noahrichards213/Interactive-chessboard/rev3/8x8/8x8.kicad_sch

## KiCad design rev3/8x8/8x8.kicad_sch (2026-08-15)

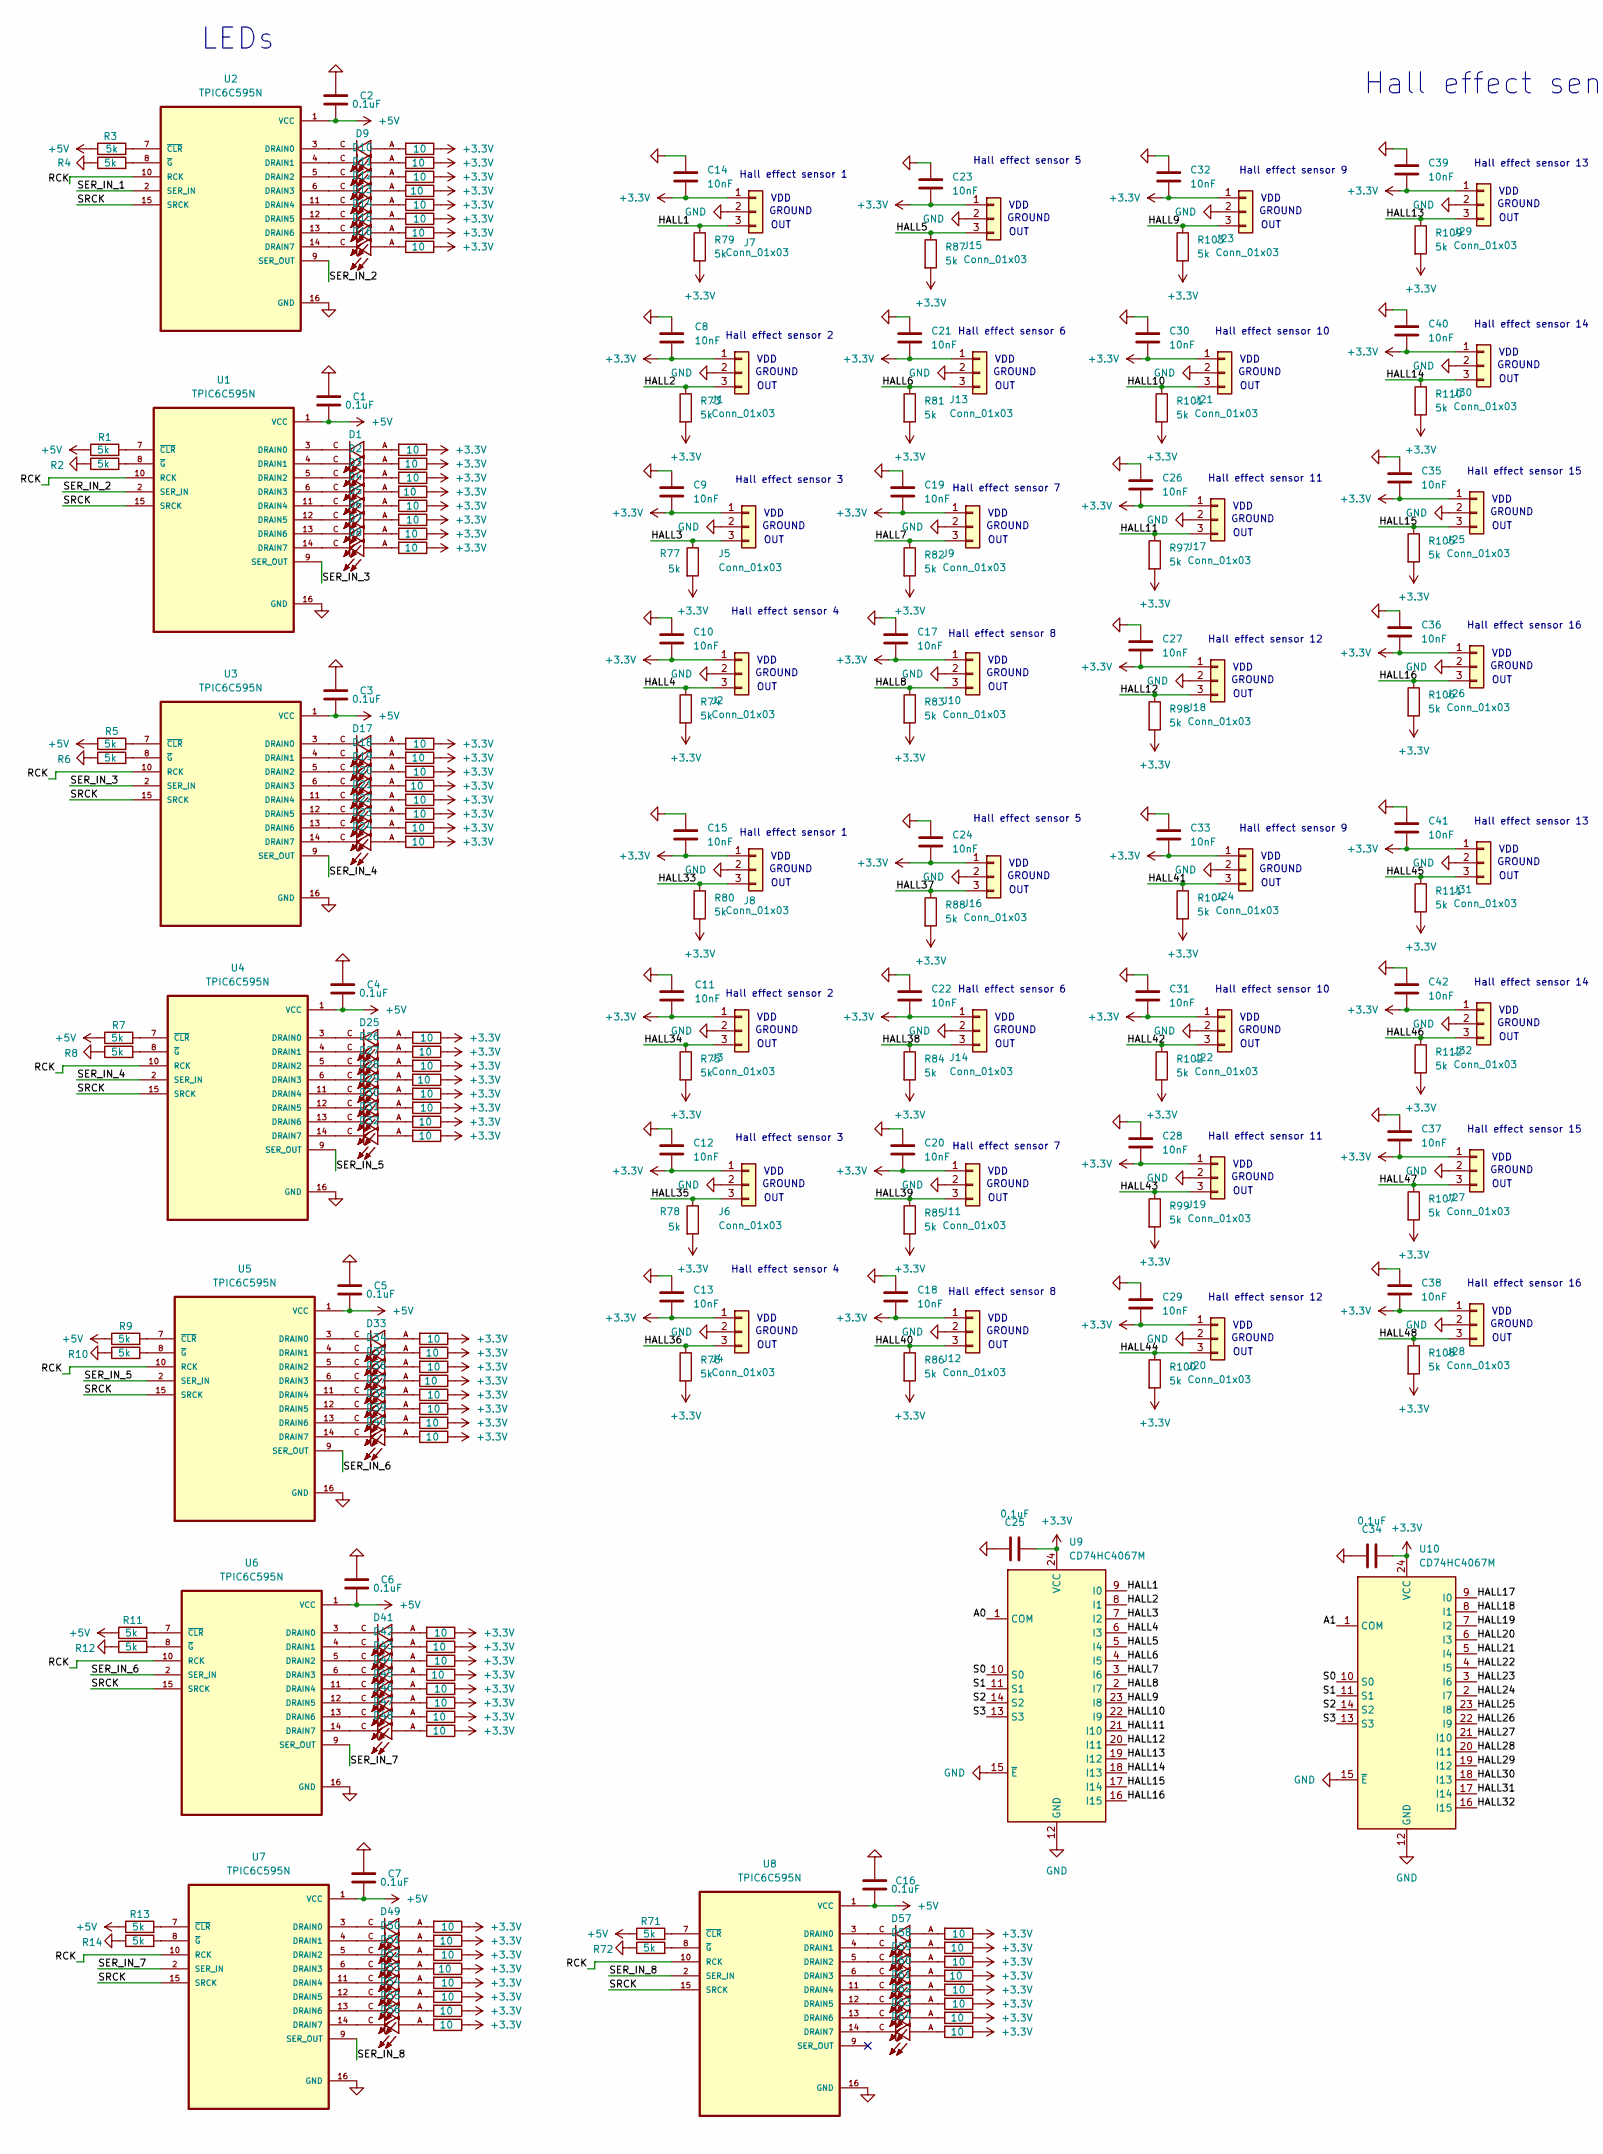
[picture p5: schematic 8x8.kicad_sch, part in row 1, column 1]

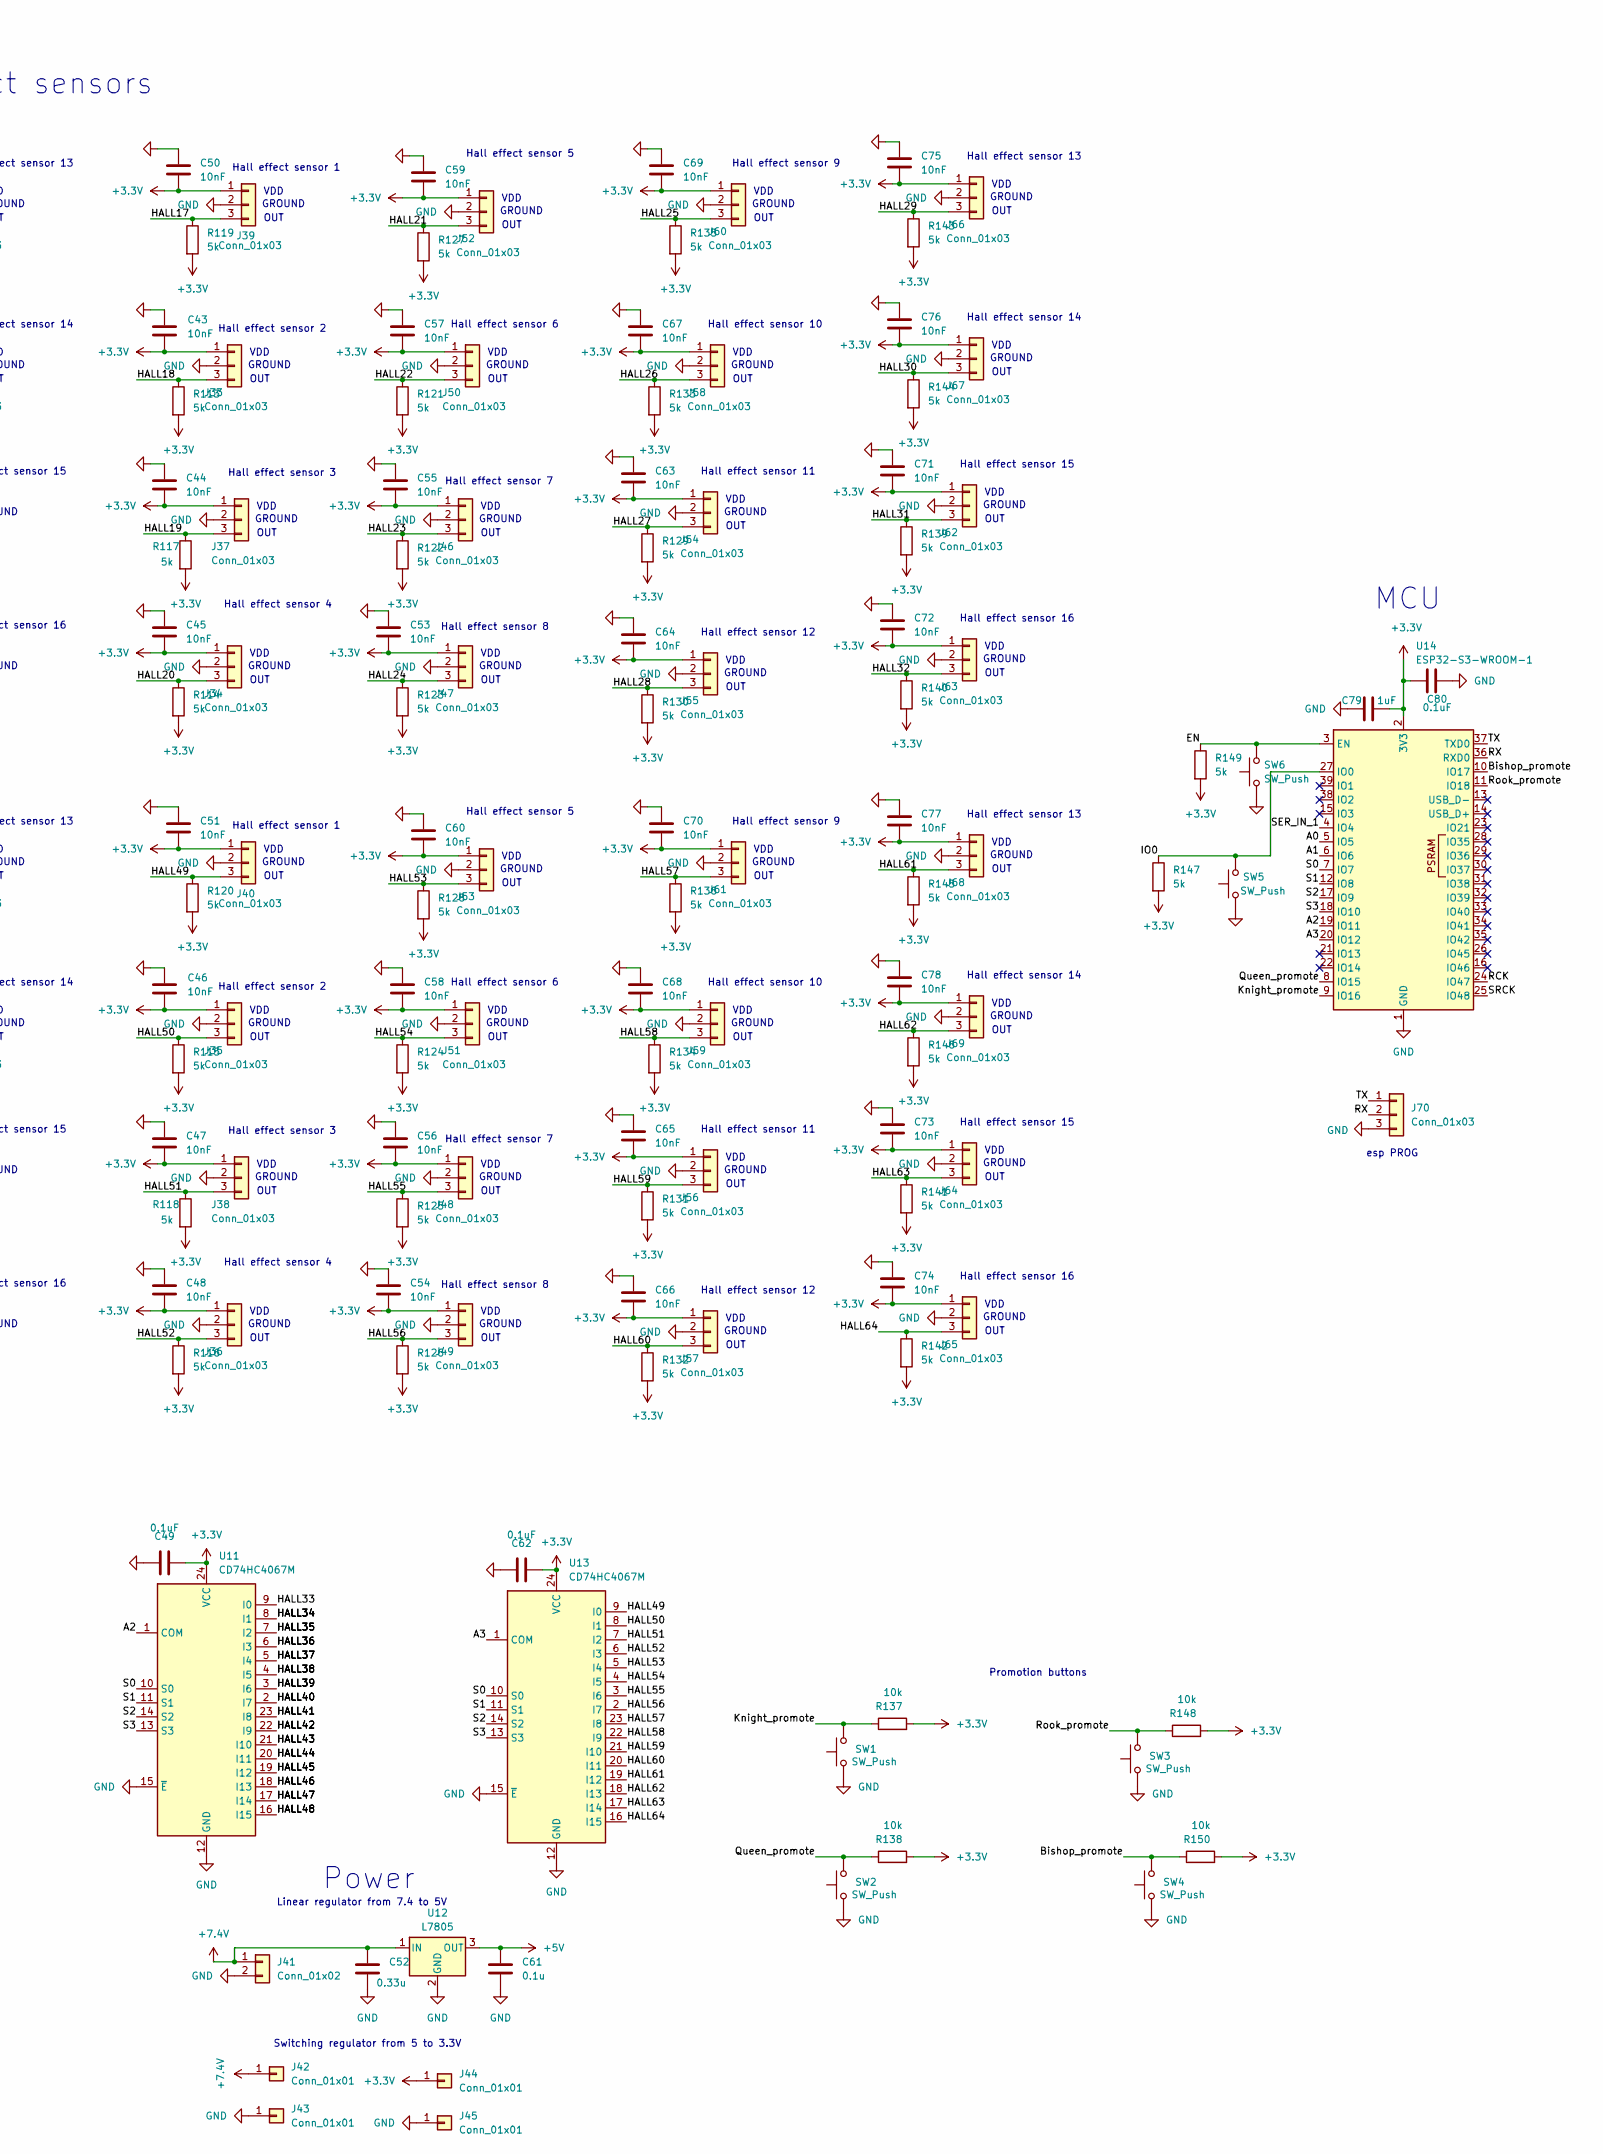
[picture p6: schematic 8x8.kicad_sch, part in row 1, column 2]

Parts:
C1, C2, C3, C4, C5, C6, C7, C16, C25, C34, C49, C62, C80: 0.1uF; C_0805_2012Metric
C8, C9, C10, C11, C12, C13, C14, C15, C17, C18, C19, C20, C21, C22, C23, C24, C26, C27, C28, C29, C30, C31, C32, C33, C35, C36, C37, C38, C39, C40, C41, C42, C43, C44, C45, C46, C47, C48, C50, C51, C53, C54, C55, C56, C57, C58, C59, C60, C63, C64, C65, C66, C67, C68, C69, C70, C71, C72, C73, C74, C75, C76, C77, C78: 10nF; C_0805_2012Metric
C52: 0.33u; C_0805_2012Metric
C61: 0.1u; C_0805_2012Metric
C79: 1uF; C_0805_2012Metric
D1, D2, D3, D4, D5, D6, D7, D8, D9, D10, D11, D12, D13, D14, D15, D16, D17, D18, D19, D20, D21, D22, D23, D24, D25, D26, D27, D28, D29, D30, D31, D32, D33, D34, D35, D36, D37, D38, D39, D40, D41, D42, D43, D44, D45, D46, D47, D48, D49, D50, D51, D52, D53, D54, D55, D56, D57, D58, D59, D60, D61, D62, D63, D64: JB5630AWT-P-H40GA0000-NZ000001; LED_JB5630AWT-P-H40GA0000-NZ000001; PARTREV 3
J1, J2, J3, J4, J5, J6, J7, J8, J9, J10, J11, J12, J13, J14, J15, J16, J17, J18, J19, J20, J21, J22, J23, J24, J25, J26, J27, J28, J29, J30, J31, J32, J33, J34, J35, J36, J37, J38, J39, J40, J46, J47, J48, J49, J50, J51, J52, J53, J54, J55, J56, J57, J58, J59, J60, J61, J62, J63, J64, J65, J66, J67, J68, J69: Conn_01x03; TSOT-3L_MLX92232LSE-AAA-002-SP_MEL
J41: Conn_01x02; AMASS_XT30U-M_1x02_P5.0mm_Vertical
J42, J43, J44, J45: Conn_01x01; PinHeader_1x01_P2.54mm_Vertical
J70: Conn_01x03; PinHeader_1x03_P2.54mm_Vertical
R1, R2, R3, R4, R5, R6, R7, R8, R9, R10, R11, R12, R13, R14, R71, R72, R73, R74, R75, R76, R77, R78, R79, R80, R81, R82, R83, R84, R85, R86, R87, R88, R97, R98, R99, R100, R101, R102, R103, R104, R105, R106, R107, R108, R109, R110, R111, R112, R113, R114, R115, R116, R117, R118, R119, R120, R121, R122, R123, R124, R125, R126, R127, R128, R129, R130, R131, R132, R133, R134, R135, R136, R139, R140, R141, R142, R143, R144, R145, R146, R147, R149: 5k; R_0805_2012Metric_Pad1.20x1.40mm_HandSolder
R15, R16, R17, R18, R19, R20, R21, R22, R23, R24, R25, R26, R27, R28, R29, R30, R31, R32, R33, R34, R35, R36, R37, R38, R39, R40, R41, R42, R43, R44, R45, R46, R47, R48, R49, R50, R51, R52, R53, R54, R55, R56, R57, R58, R59, R60, R61, R62, R63, R64, R65, R66, R67, R68, R69, R70, R89, R90, R91, R92, R93, R94, R95, R96: 10; R_0805_2012Metric_Pad1.20x1.40mm_HandSolder
R137, R138, R148, R150: 10k; R_0805_2012Metric_Pad1.20x1.40mm_HandSolder
SW1, SW2, SW3, SW4, SW5, SW6: SW_Push; SW_SPST_SKQG_WithStem
U1, U2, U3, U4, U5, U6, U7, U8: TPIC6C595N; SOIC127P600X175-16N
U9, U10, U11, U13: CD74HC4067M; SOIC127P1030X265-24N
U12: L7805; L7805CDTTR
U14: ESP32-S3-WROOM-1

Connections:
+3.3V: C8.2, C9.2, C10.2, C11.2, C12.2, C13.2, C14.2, C15.2, C17.2, C18.2, C19.2, C20.2, C21.2, C22.2, C23.2, C24.2, C25.2, C26.2, C27.2, C28.2, C29.2, C30.2, C31.2, C32.2, C33.2, C34.2, C35.2, C36.2, C37.2, C38.2, C39.2, C40.2, C41.2, C42.2, C43.2, C44.2, C45.2, C46.2, C47.2, C48.2, C49.2, C50.2, C51.2, C53.2, C54.2, C55.2, C56.2, C57.2, C58.2, C59.2, C60.2, C62.2, C63.2, C64.2, C65.2, C66.2, C67.2, C68.2, C69.2, C70.2, C71.2, C72.2, C73.2, C74.2, C75.2, C76.2, C77.2, C78.2, C79.2, C80.2, J1.1, J2.1, J3.1, J4.1, J5.1, J6.1, J7.1, J8.1, J9.1, J10.1, J11.1, J12.1, J13.1, J14.1, J15.1, J16.1, J17.1, J18.1, J19.1, J20.1, J21.1, J22.1, J23.1, J24.1, J25.1, J26.1, J27.1, J28.1, J29.1, J30.1, J31.1, J32.1, J33.1, J34.1, J35.1, J36.1, J37.1, J38.1, J39.1, J40.1, J44.1, J46.1, J47.1, J48.1, J49.1, J50.1, J51.1, J52.1, J53.1, J54.1, J55.1, J56.1, J57.1, J58.1, J59.1, J60.1, J61.1, J62.1, J63.1, J64.1, J65.1, J66.1, J67.1, J68.1, J69.1, R15.1, R16.1, R17.1, R18.1, R19.1, R20.1, R21.1, R22.1, R23.1, R24.1, R25.1, R26.1, R27.1, R28.1, R29.1, R30.1, R31.1, R32.1, R33.1, R34.1, R35.1, R36.1, R37.1, R38.1, R39.1, R40.1, R41.1, R42.1, R43.1, R44.1, R45.1, R46.1, R47.1, R48.1, R49.1, R50.1, R51.1, R52.1, R53.1, R54.1, R55.1, R56.1, R57.1, R58.1, R59.1, R60.1, R61.1, R62.1, R63.1, R64.1, R65.1, R66.1, R67.1, R68.1, R69.1, R70.1, R73.2, R74.2, R75.2, R76.2, R77.2, R78.2, R79.2, R80.2, R81.2, R82.2, R83.2, R84.2, R85.2, R86.2, R87.2, R88.2, R89.1, R90.1, R91.1, R92.1, R93.1, R94.1, R95.1, R96.1, R97.2, R98.2, R99.2, R100.2, R101.2, R102.2, R103.2, R104.2, R105.2, R106.2, R107.2, R108.2, R109.2, R110.2, R111.2, R112.2, R113.2, R114.2, R115.2, R116.2, R117.2, R118.2, R119.2, R120.2, R121.2, R122.2, R123.2, R124.2, R125.2, R126.2, R127.2, R128.2, R129.2, R130.2, R131.2, R132.2, R133.2, R134.2, R135.2, R136.2, R137.2, R138.2, R139.2, R140.2, R141.2, R142.2, R143.2, R144.2, R145.2, R146.2, R147.2, R148.2, R149.2, R150.2, U9.24 (VCC), U10.24 (VCC), U11.24 (VCC), U13.24 (VCC), U14.2 (3V3)
+5V: C1.2, C2.2, C3.2, C4.2, C5.2, C6.2, C7.2, C16.2, C61.1, R1.1, R3.1, R5.1, R7.1, R9.1, R11.1, R13.1, R71.1, U1.1 (VCC), U2.1 (VCC), U3.1 (VCC), U4.1 (VCC), U5.1 (VCC), U6.1 (VCC), U7.1 (VCC), U8.1 (VCC), U12.3 (OUT)
+7.4V: C52.1, J41.1, J42.1, U12.1 (IN)
A0: U9.1 (COM), U14.5 (IO5)
A1: U10.1 (COM), U14.6 (IO6)
A2: U11.1 (COM), U14.19 (IO11)
A3: U13.1 (COM), U14.20 (IO12)
Bishop_promote: R150.1, SW4.2, U14.10 (IO17)
EN: R149.1, SW6.2, U14.3 (EN)
GND: C1.1, C2.1, C3.1, C4.1, C5.1, C6.1, C7.1, C8.1, C9.1, C10.1, C11.1, C12.1, C13.1, C14.1, C15.1, C16.1, C17.1, C18.1, C19.1, C20.1, C21.1, C22.1, C23.1, C24.1, C25.1, C26.1, C27.1, C28.1, C29.1, C30.1, C31.1, C32.1, C33.1, C34.1, C35.1, C36.1, C37.1, C38.1, C39.1, C40.1, C41.1, C42.1, C43.1, C44.1, C45.1, C46.1, C47.1, C48.1, C49.1, C50.1, C51.1, C52.2, C53.1, C54.1, C55.1, C56.1, C57.1, C58.1, C59.1, C60.1, C61.2, C62.1, C63.1, C64.1, C65.1, C66.1, C67.1, C68.1, C69.1, C70.1, C71.1, C72.1, C73.1, C74.1, C75.1, C76.1, C77.1, C78.1, C79.1, C80.1, J1.2, J2.2, J3.2, J4.2, J5.2, J6.2, J7.2, J8.2, J9.2, J10.2, J11.2, J12.2, J13.2, J14.2, J15.2, J16.2, J17.2, J18.2, J19.2, J20.2, J21.2, J22.2, J23.2, J24.2, J25.2, J26.2, J27.2, J28.2, J29.2, J30.2, J31.2, J32.2, J33.2, J34.2, J35.2, J36.2, J37.2, J38.2, J39.2, J40.2, J41.2, J43.1, J45.1, J46.2, J47.2, J48.2, J49.2, J50.2, J51.2, J52.2, J53.2, J54.2, J55.2, J56.2, J57.2, J58.2, J59.2, J60.2, J61.2, J62.2, J63.2, J64.2, J65.2, J66.2, J67.2, J68.2, J69.2, J70.3, R2.1, R4.1, R6.1, R8.1, R10.1, R12.1, R14.1, R72.1, SW1.1, SW2.1, SW3.1, SW4.1, SW5.1, SW6.1, U1.16 (GND), U2.16 (GND), U3.16 (GND), U4.16 (GND), U5.16 (GND), U6.16 (GND), U7.16 (GND), U8.16 (GND), U9.12 (GND), U9.15 (~E), U10.12 (GND), U10.15 (~E), U11.12 (GND), U11.15 (~E), U12.2 (GND), U13.12 (GND), U13.15 (~E), U14.1 (GND), U14.40 (GND), U14.41 (GND)
HALL1: J7.3, R79.1, U9.9 (I0)
HALL2: J1.3, R73.1, U9.8 (I1)
HALL3: J5.3, R77.1, U9.7 (I2)
HALL4: J2.3, R74.1, U9.6 (I3)
HALL5: J15.3, R87.1, U9.5 (I4)
HALL6: J13.3, R81.1, U9.4 (I5)
HALL7: J9.3, R82.1, U9.3 (I6)
HALL8: J10.3, R83.1, U9.2 (I7)
HALL9: J23.3, R103.1, U9.23 (I8)
HALL10: J21.3, R101.1, U9.22 (I9)
HALL11: J17.3, R97.1, U9.21 (I10)
HALL12: J18.3, R98.1, U9.20 (I11)
HALL13: J29.3, R109.1, U9.19 (I12)
HALL14: J30.3, R110.1, U9.18 (I13)
HALL15: J25.3, R105.1, U9.17 (I14)
HALL16: J26.3, R106.1, U9.16 (I15)
HALL17: J39.3, R119.1, U10.9 (I0)
HALL18: J33.3, R113.1, U10.8 (I1)
HALL19: J37.3, R117.1, U10.7 (I2)
HALL20: J34.3, R114.1, U10.6 (I3)
HALL21: J52.3, R127.1, U10.5 (I4)
HALL22: J50.3, R121.1, U10.4 (I5)
HALL23: J46.3, R122.1, U10.3 (I6)
HALL24: J47.3, R123.1, U10.2 (I7)
HALL25: J60.3, R135.1, U10.23 (I8)
HALL26: J58.3, R133.1, U10.22 (I9)
HALL27: J54.3, R129.1, U10.21 (I10)
HALL28: J55.3, R130.1, U10.20 (I11)
HALL29: J66.3, R143.1, U10.19 (I12)
HALL30: J67.3, R144.1, U10.18 (I13)
HALL31: J62.3, R139.1, U10.17 (I14)
HALL32: J63.3, R140.1, U10.16 (I15)
HALL33: J8.3, R80.1, U11.9 (I0)
HALL34: J3.3, R75.1, U11.8 (I1)
HALL35: J6.3, R78.1, U11.7 (I2)
HALL36: J4.3, R76.1, U11.6 (I3)
HALL37: J16.3, R88.1, U11.5 (I4)
HALL38: J14.3, R84.1, U11.4 (I5)
HALL39: J11.3, R85.1, U11.3 (I6)
HALL40: J12.3, R86.1, U11.2 (I7)
HALL41: J24.3, R104.1, U11.23 (I8)
HALL42: J22.3, R102.1, U11.22 (I9)
HALL43: J19.3, R99.1, U11.21 (I10)
HALL44: J20.3, R100.1, U11.20 (I11)
HALL45: J31.3, R111.1, U11.19 (I12)
HALL46: J32.3, R112.1, U11.18 (I13)
HALL47: J27.3, R107.1, U11.17 (I14)
HALL48: J28.3, R108.1, U11.16 (I15)
HALL49: J40.3, R120.1, U13.9 (I0)
HALL50: J35.3, R115.1, U13.8 (I1)
HALL51: J38.3, R118.1, U13.7 (I2)
HALL52: J36.3, R116.1, U13.6 (I3)
HALL53: J53.3, R128.1, U13.5 (I4)
HALL54: J51.3, R124.1, U13.4 (I5)
HALL55: J48.3, R125.1, U13.3 (I6)
HALL56: J49.3, R126.1, U13.2 (I7)
HALL57: J61.3, R136.1, U13.23 (I8)
HALL58: J59.3, R134.1, U13.22 (I9)
HALL59: J56.3, R131.1, U13.21 (I10)
HALL60: J57.3, R132.1, U13.20 (I11)
HALL61: J68.3, R145.1, U13.19 (I12)
HALL62: J69.3, R146.1, U13.18 (I13)
HALL63: J64.3, R141.1, U13.17 (I14)
HALL64: J65.3, R142.1, U13.16 (I15)
IO0: R147.1, SW5.2, U14.27 (IO0)
Knight_promote: R137.1, SW1.2, U14.9 (IO16)
unnamed: D1.A, R15.2
unnamed: D1.C, U1.3 (DRAIN0)
unnamed: D2.A, R16.2
unnamed: D2.C, U1.4 (DRAIN1)
unnamed: D3.A, R17.2
unnamed: D3.C, U1.5 (DRAIN2)
unnamed: D4.A, R18.2
unnamed: D4.C, U1.6 (DRAIN3)
unnamed: D5.A, R19.2
unnamed: D5.C, U1.11 (DRAIN4)
unnamed: D6.A, R20.2
unnamed: D6.C, U1.12 (DRAIN5)
unnamed: D7.A, R21.2
unnamed: D7.C, U1.13 (DRAIN6)
unnamed: D8.A, R22.2
unnamed: D8.C, U1.14 (DRAIN7)
unnamed: D9.A, R23.2
unnamed: D9.C, U2.3 (DRAIN0)
unnamed: D10.A, R24.2
unnamed: D10.C, U2.4 (DRAIN1)
unnamed: D11.A, R25.2
unnamed: D11.C, U2.5 (DRAIN2)
unnamed: D12.A, R26.2
unnamed: D12.C, U2.6 (DRAIN3)
unnamed: D13.A, R27.2
unnamed: D13.C, U2.11 (DRAIN4)
unnamed: D14.A, R28.2
unnamed: D14.C, U2.12 (DRAIN5)
unnamed: D15.A, R29.2
unnamed: D15.C, U2.13 (DRAIN6)
unnamed: D16.A, R30.2
unnamed: D16.C, U2.14 (DRAIN7)
unnamed: D17.A, R31.2
unnamed: D17.C, U3.3 (DRAIN0)
unnamed: D18.A, R32.2
unnamed: D18.C, U3.4 (DRAIN1)
unnamed: D19.A, R33.2
unnamed: D19.C, U3.5 (DRAIN2)
unnamed: D20.A, R34.2
unnamed: D20.C, U3.6 (DRAIN3)
unnamed: D21.A, R35.2
unnamed: D21.C, U3.11 (DRAIN4)
unnamed: D22.A, R36.2
unnamed: D22.C, U3.12 (DRAIN5)
unnamed: D23.A, R37.2
unnamed: D23.C, U3.13 (DRAIN6)
unnamed: D24.A, R38.2
unnamed: D24.C, U3.14 (DRAIN7)
unnamed: D25.A, R39.2
unnamed: D25.C, U4.3 (DRAIN0)
unnamed: D26.A, R40.2
unnamed: D26.C, U4.4 (DRAIN1)
unnamed: D27.A, R41.2
unnamed: D27.C, U4.5 (DRAIN2)
unnamed: D28.A, R42.2
unnamed: D28.C, U4.6 (DRAIN3)
unnamed: D29.A, R43.2
unnamed: D29.C, U4.11 (DRAIN4)
unnamed: D30.A, R44.2
unnamed: D30.C, U4.12 (DRAIN5)
unnamed: D31.A, R45.2
unnamed: D31.C, U4.13 (DRAIN6)
unnamed: D32.A, R46.2
unnamed: D32.C, U4.14 (DRAIN7)
unnamed: D33.A, R47.2
unnamed: D33.C, U5.3 (DRAIN0)
unnamed: D34.A, R48.2
unnamed: D34.C, U5.4 (DRAIN1)
unnamed: D35.A, R49.2
unnamed: D35.C, U5.5 (DRAIN2)
unnamed: D36.A, R50.2
unnamed: D36.C, U5.6 (DRAIN3)
unnamed: D37.A, R51.2
unnamed: D37.C, U5.11 (DRAIN4)
unnamed: D38.A, R52.2
unnamed: D38.C, U5.12 (DRAIN5)
unnamed: D39.A, R53.2
unnamed: D39.C, U5.13 (DRAIN6)
unnamed: D40.A, R54.2
unnamed: D40.C, U5.14 (DRAIN7)
unnamed: D41.A, R55.2
unnamed: D41.C, U6.3 (DRAIN0)
unnamed: D42.A, R56.2
unnamed: D42.C, U6.4 (DRAIN1)
unnamed: D43.A, R57.2
unnamed: D43.C, U6.5 (DRAIN2)
unnamed: D44.A, R58.2
unnamed: D44.C, U6.6 (DRAIN3)
unnamed: D45.A, R59.2
unnamed: D45.C, U6.11 (DRAIN4)
unnamed: D46.A, R60.2
unnamed: D46.C, U6.12 (DRAIN5)
unnamed: D47.A, R61.2
unnamed: D47.C, U6.13 (DRAIN6)
unnamed: D48.A, R62.2
unnamed: D48.C, U6.14 (DRAIN7)
unnamed: D49.A, R63.2
unnamed: D49.C, U7.3 (DRAIN0)
unnamed: D50.A, R64.2
unnamed: D50.C, U7.4 (DRAIN1)
unnamed: D51.A, R65.2
unnamed: D51.C, U7.5 (DRAIN2)
unnamed: D52.A, R66.2
unnamed: D52.C, U7.6 (DRAIN3)
unnamed: D53.A, R67.2
unnamed: D53.C, U7.11 (DRAIN4)
unnamed: D54.A, R68.2
unnamed: D54.C, U7.12 (DRAIN5)
unnamed: D55.A, R69.2
unnamed: D55.C, U7.13 (DRAIN6)
unnamed: D56.A, R70.2
unnamed: D56.C, U7.14 (DRAIN7)
unnamed: D57.A, R89.2
unnamed: D57.C, U8.3 (DRAIN0)
unnamed: D58.A, R90.2
unnamed: D58.C, U8.4 (DRAIN1)
unnamed: D59.A, R91.2
unnamed: D59.C, U8.5 (DRAIN2)
unnamed: D60.A, R92.2
unnamed: D60.C, U8.6 (DRAIN3)
unnamed: D61.A, R93.2
unnamed: D61.C, U8.11 (DRAIN4)
unnamed: D62.A, R94.2
unnamed: D62.C, U8.12 (DRAIN5)
unnamed: D63.A, R95.2
unnamed: D63.C, U8.13 (DRAIN6)
unnamed: D64.A, R96.2
unnamed: D64.C, U8.14 (DRAIN7)
unnamed: R1.2, U1.7 (~CLR)
unnamed: R2.2, U1.8 (~G)
unnamed: R3.2, U2.7 (~CLR)
unnamed: R4.2, U2.8 (~G)
unnamed: R5.2, U3.7 (~CLR)
unnamed: R6.2, U3.8 (~G)
unnamed: R7.2, U4.7 (~CLR)
unnamed: R8.2, U4.8 (~G)
unnamed: R9.2, U5.7 (~CLR)
unnamed: R10.2, U5.8 (~G)
unnamed: R11.2, U6.7 (~CLR)
unnamed: R12.2, U6.8 (~G)
unnamed: R13.2, U7.7 (~CLR)
unnamed: R14.2, U7.8 (~G)
unnamed: R71.2, U8.7 (~CLR)
unnamed: R72.2, U8.8 (~G)
Queen_promote: R138.1, SW2.2, U14.8 (IO15)
RCK: U1.10 (RCK), U2.10 (RCK), U3.10 (RCK), U4.10 (RCK), U5.10 (RCK), U6.10 (RCK), U7.10 (RCK), U8.10 (RCK), U14.24 (IO47)
RX: J70.2, U14.36 (RXD0)
Rook_promote: R148.1, SW3.2, U14.11 (IO18)
S0: U9.10 (S0), U10.10 (S0), U11.10 (S0), U13.10 (S0), U14.7 (IO7)
S1: U9.11 (S1), U10.11 (S1), U11.11 (S1), U13.11 (S1), U14.12 (IO8)
S2: U9.14 (S2), U10.14 (S2), U11.14 (S2), U13.14 (S2), U14.17 (IO9)
S3: U9.13 (S3), U10.13 (S3), U11.13 (S3), U13.13 (S3), U14.18 (IO10)
SER_IN_1: U2.2 (SER_IN), U14.4 (IO4)
SER_IN_2: U1.2 (SER_IN), U2.9 (SER_OUT)
SER_IN_3: U1.9 (SER_OUT), U3.2 (SER_IN)
SER_IN_4: U3.9 (SER_OUT), U4.2 (SER_IN)
SER_IN_5: U4.9 (SER_OUT), U5.2 (SER_IN)
SER_IN_6: U5.9 (SER_OUT), U6.2 (SER_IN)
SER_IN_7: U6.9 (SER_OUT), U7.2 (SER_IN)
SER_IN_8: U7.9 (SER_OUT), U8.2 (SER_IN)
SRCK: U1.15 (SRCK), U2.15 (SRCK), U3.15 (SRCK), U4.15 (SRCK), U5.15 (SRCK), U6.15 (SRCK), U7.15 (SRCK), U8.15 (SRCK), U14.25 (IO48)
TX: J70.1, U14.37 (TXD0)

Notes on the sheet:
Hall effect sensor 16
Hall effect sensor 1
GROUND
Hall effect sensor 9
VDD
OUT
Hall effect sensor 12
Hall effect sensor 6
Hall effect sensor 8
LEDs
Hall effect sensor 10
Hall effect sensor 15
Hall effect sensor 11
Hall effect sensor 5
Hall effect sensor 7
Hall effect sensor 2
Hall effect sensor 3
Hall effect sensor 4
Linear regulator from 7.4 to 5V
Hall effect sensors
Hall effect sensor 13
Power
Promotion buttons
Hall effect sensor 14
Switching regulator from 5 to 3.3V
MCU
esp PROG
