noahrichards213/Interactive-chessboard/rev3/8x8 code w extern/availablemoves.h

#ifndef AVAILABLEMOVES
#define AVAILABLEMOVES

#ifdef __cplusplus
extern "C" {
#endif

#include "arraysize.h"
#include "constantsandstructs.h"

// returns array of legal moves
int* rookMoves(Piece piece);
int* bishopMoves(Piece piece);
int* queenMoves(Piece piece);
int* knightMoves(Piece piece);
int* pawnMoves(Piece piece);
int* kingMoves(Piece piece);

#ifdef __cplusplus
}
#endif

#endif
