noahrichards213/Interactive-chessboard/rev3/8x8 code w extern/legalinput.h

#ifndef LEGALINPUT
#define LEGALINPUT

#ifdef __cplusplus
extern "C" {
#endif

#include <stdbool.h>

#include "constantsandstructs.h"

Piece legalSource(char file, int rank, int colour);
int legalDest(char file, int rank, char fileSource, int rankSource, int colour);

#ifdef __cplusplus
}
#endif

#endif
