noahrichards213/Interactive-chessboard/rev3/8x8 code w extern/legalmoveandcapture.h

#ifndef LEGALMOVEANDCAPTURE
#define LEGALMOVEANDCAPTURE

#ifdef __cplusplus
extern "C" {
#endif

#include "constantsandstructs.h"
// inserts/updates piece info
void changeAvailableMoves(Piece* piece, int colour);

// checks is there is an available move
bool checkLegalMoves(int turn);

#ifdef __cplusplus
}
#endif

#endif
