noahrichards213/Interactive-chessboard/rev3/8x8 code w extern/promotion.h

#ifndef PROMOTION
#define PROMOTION

#ifdef __cplusplus
extern "C" {
#endif

#include "constantsandstructs.h"

Piece executePromotion(int colour, int rankDest, char fileDest);

#ifdef __cplusplus
}
#endif

#endif
