noahrichards213/Interactive-chessboard/rev3/8x8 code w extern/printing.h

#ifndef PRINTING
#define PRINTING

#ifdef __cplusplus
extern "C" {
#endif

#include "constantsandstructs.h"

// printing board in terminal for user to see
void printBoard(Piece board[8][8]);

// printing all info in table
void printLegalMoves();

//printing piece info
void printPieceInfo(Piece piece);

#ifdef __cplusplus
}
#endif

#endif
