noahrichards213/Interactive-chessboard/rev3/8x8 code w extern/enpassant.c

#include "enpassant.h"

#include <math.h>
#include <stdbool.h>
#include <stdio.h>
#include <stdlib.h>

#include "arraysize.h"
#include "printing.h"

extern Piece board[8][8];

void removeEnPassant() {
  for (int i = 0; i < 8; i++) {
    for (int j = 0; j < 8; j++) {
      int size = arraySize(board[i][j].availableMoves);
      for (int k = 0; k < size; k++) {
        // has en passant move
        if (board[i][j].availableMoves[k] >= 10000) {
          board[i][j].availableMoves[k] = EN_PASSANT;
        }
      }
    }
  }
}

// colour is the pawn that moved two squares
// rank and file is the square that it moved to (use actual inputted values)
void addEnPassant(Piece piece, int rank, char file) {
  int colour = piece.colour;
  char enemyPawn;

  // old rank - new rank
  int difference = abs(piece.rank - rank);

  printf("this is the difference: %d\n", difference);

  // if pawn did not move two squares then we don't need this function
  if (difference != 2) {
    printf("We did return\n");
    return;
  }

  printf("We didn't return\n");

  // white is 1, black is 0
  enemyPawn = colour ? 'p' : 'P';
  // we know that if the pawn successfully moved two
  // squares nothing can be blocking it

  // STILL NEED TO DO MAKE THIS . IT'S CURRENTLY NONSENSE
  //  left side en passant

  int boardRank = 8 - rank;
  int boardFile = file - 97;

  // only one en passant move is possible per turn per peace
  int capacityMoves = 1;
  int* enPassantMove = malloc(sizeof(int) * capacityMoves);

  // this is immediately recognized and deal with in change avialable moves
  if (board[boardRank][boardFile - 1].type == enemyPawn) {
    // creating en passant array move
    //  multiples the enpassant square by 1000 to differentiate from reg move
    enPassantMove[0] = (boardRank * 10 + (boardFile)) * 1000;
    board[boardRank][boardFile - 1].availableMoves = enPassantMove;
  }

  if (board[boardRank][boardFile + 1].type == enemyPawn) {
    // creating en passant array move
    //  multiples the enpassant square by 1000 to differentiate from reg move
    enPassantMove[0] = (boardRank * 10 + (boardFile)) * 1000;
    board[boardRank][boardFile + 1].availableMoves = enPassantMove;
  }

  return;
}
