noahrichards213/Interactive-chessboard/rev3/test_written_before_8x8_arrived/removecheck.h

#ifndef REMOVECHECK
#define REMOVECHECK

#ifdef __cplusplus
extern "C" {
#endif

#include <stdbool.h>
#include "constantsandstructs.h"

int removeCheck(Piece piece, int availableMoveIndex, int testedMove);
void deepCopyPiece(Piece *dest, Piece *src);

#ifdef __cplusplus
}
#endif

#endif
